tino1b2be/ST080/Docs/Case/Dimensions/instrument.png

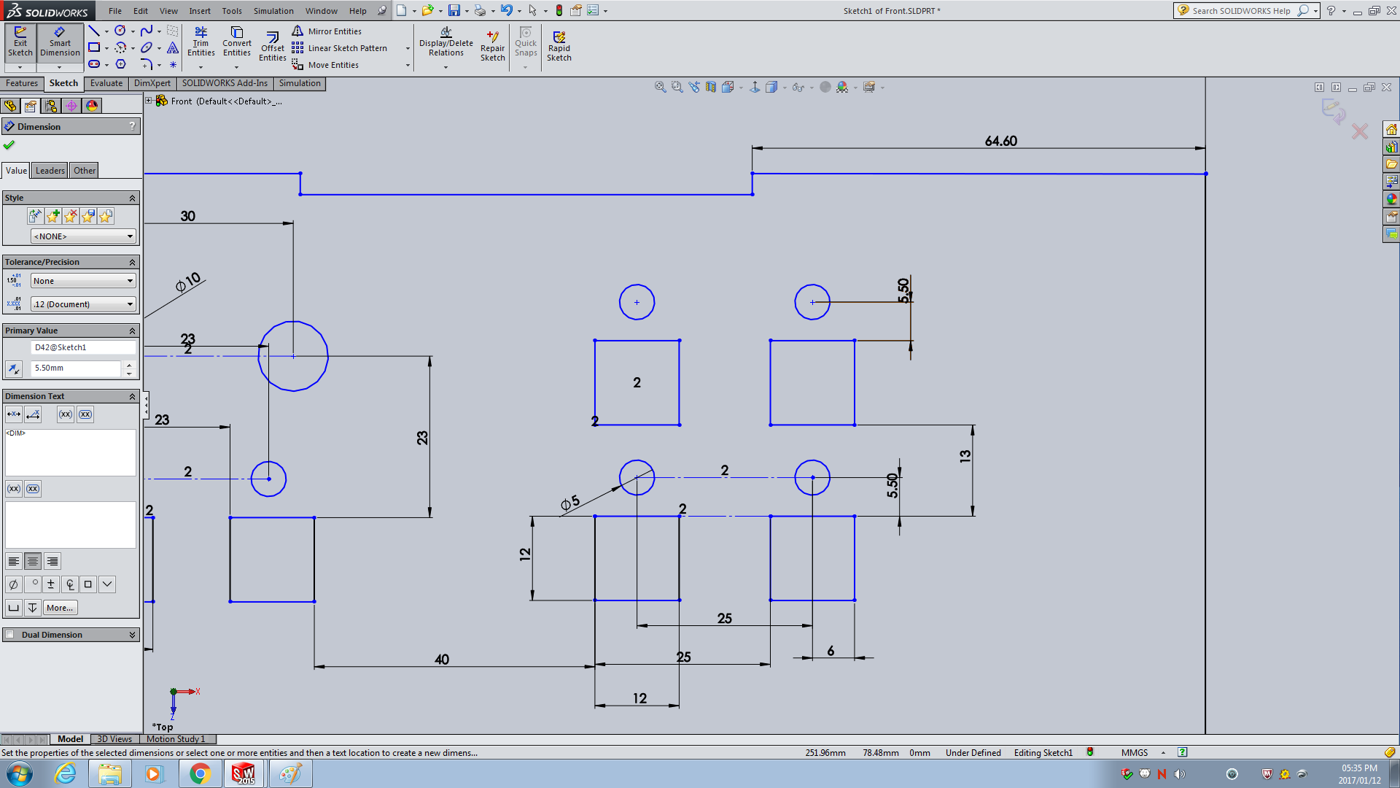
Docs/Case/Dimensions/instrument.png
