tino1b2be/ST080/Docs/Case/Dimensions/lcd.png

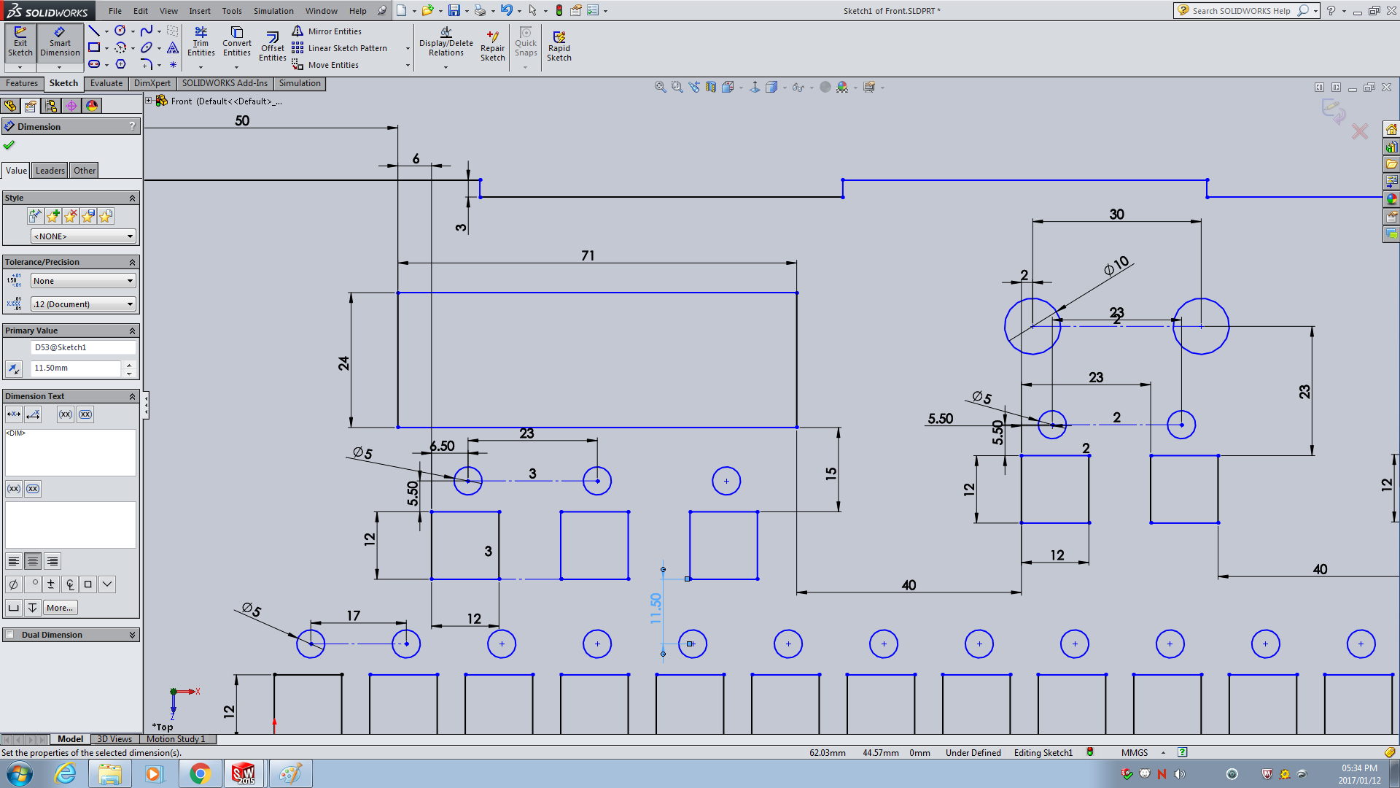
Docs/Case/Dimensions/lcd.png
