tino1b2be/ST080/Docs/Case/Dimensions/rack.png

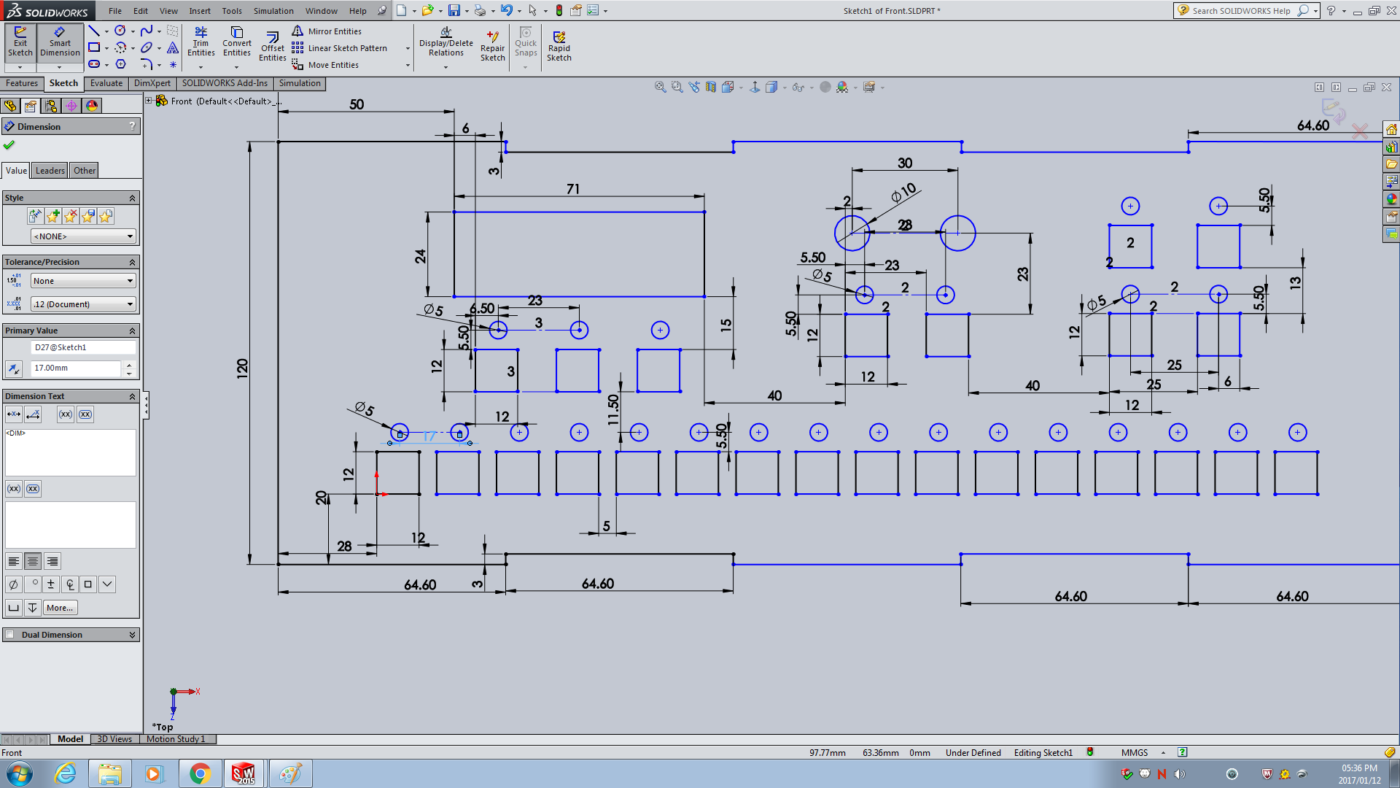
Docs/Case/Dimensions/rack.png
