tino1b2be/ST080/Docs/Case/Dimensions/tempo.png

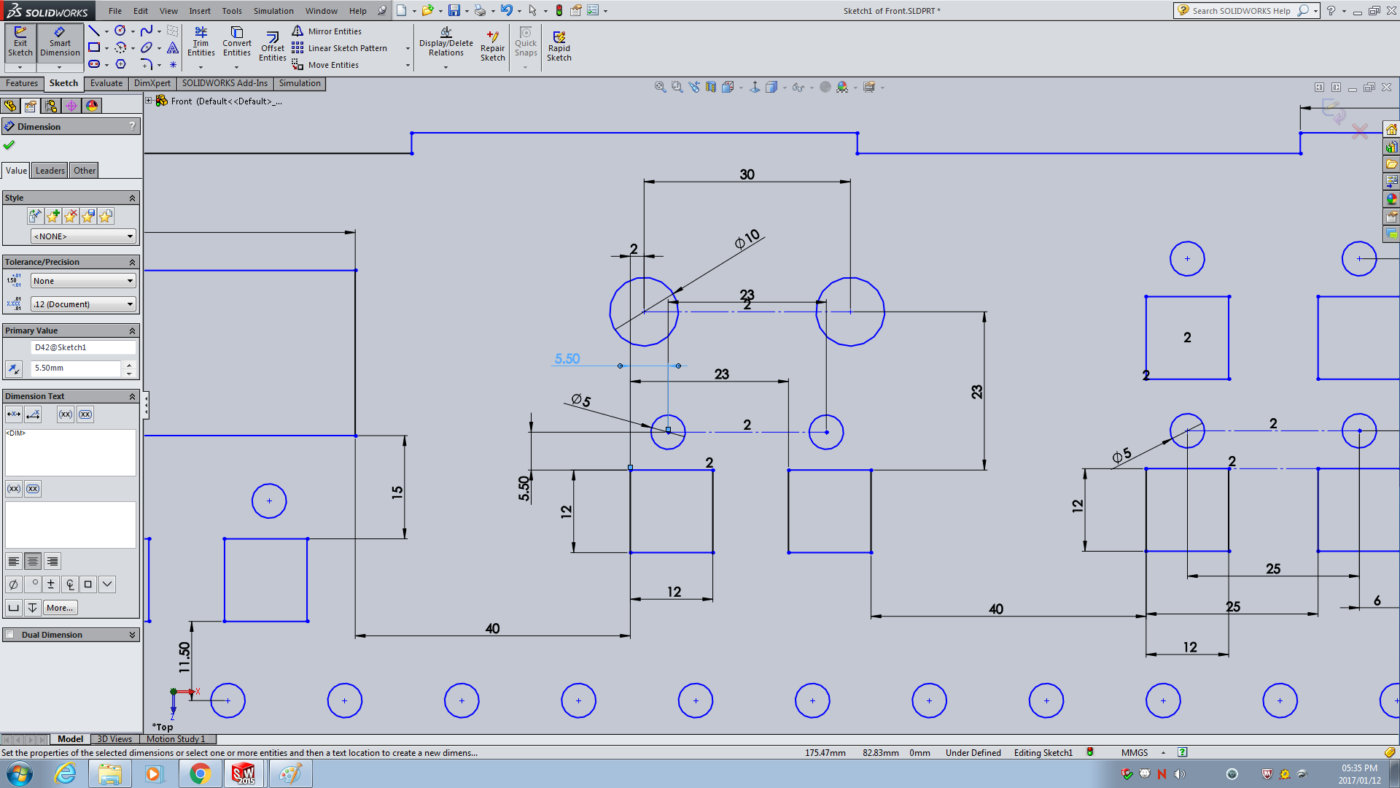
Docs/Case/Dimensions/tempo.png
