tino1b2be/ST080/Docs/Case/Dimensions/whole.png

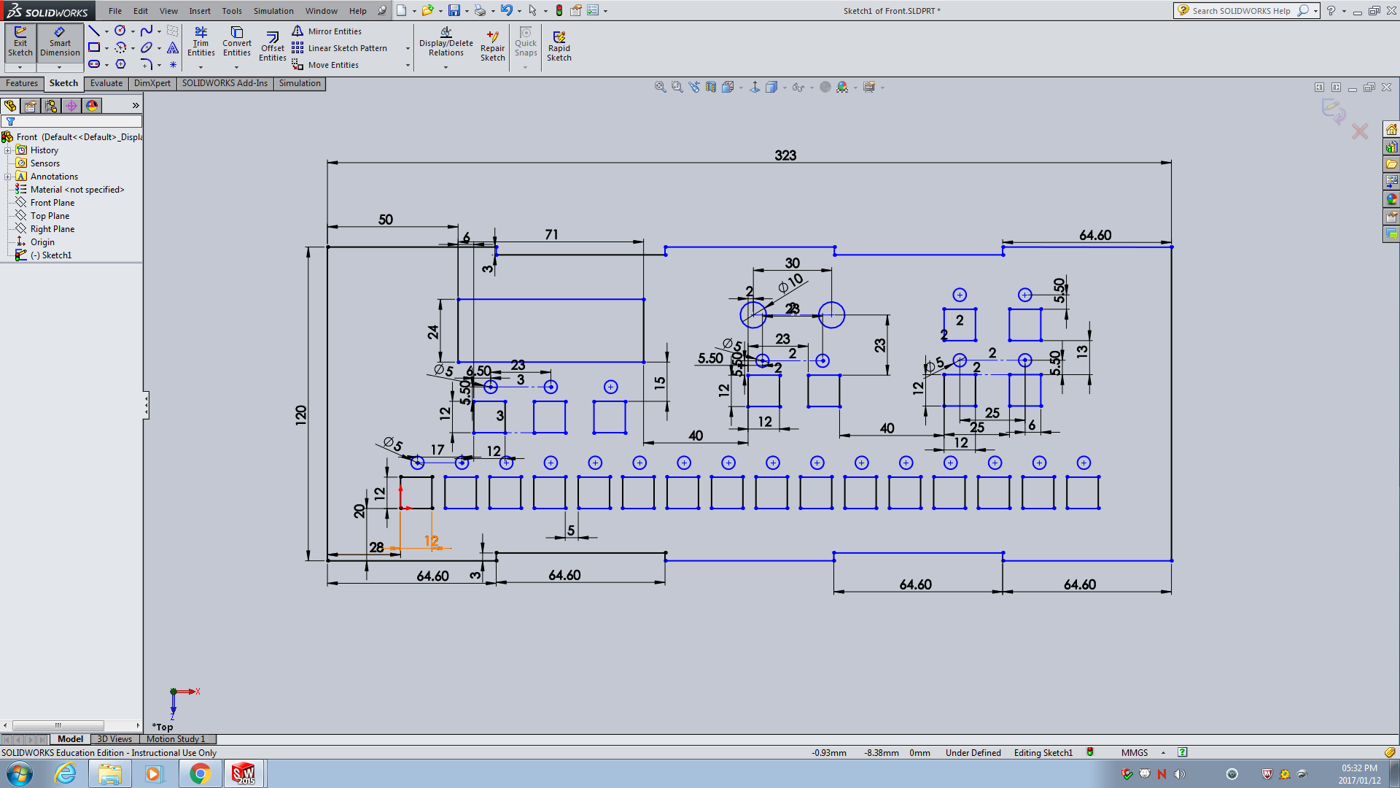
Docs/Case/Dimensions/whole.png
