tino1b2be/ST080/Docs/Case/Views/Back.PNG

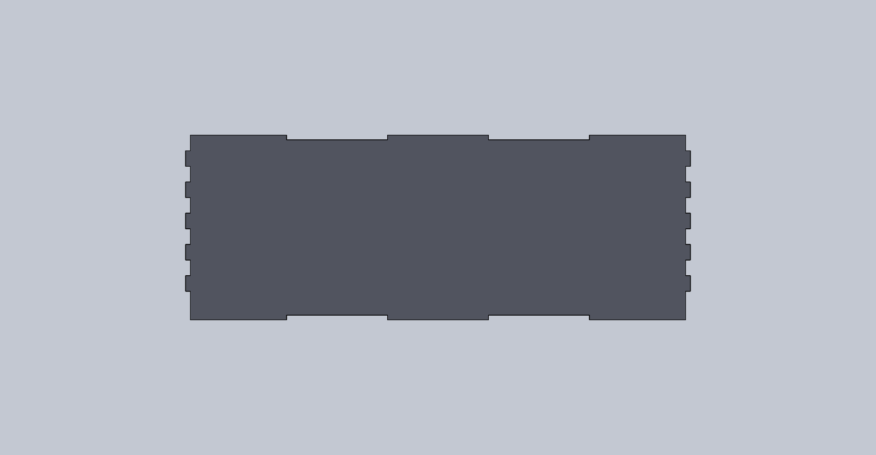
Docs/Case/Views/Back.PNG
