tino1b2be/ST080/Docs/Case/Views/Bottom.PNG

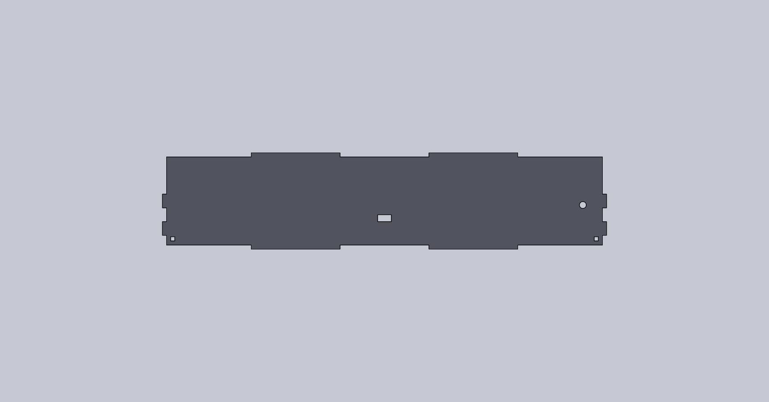
Docs/Case/Views/Bottom.PNG
