tino1b2be/ST080/Docs/Case/Views/Connector.PNG

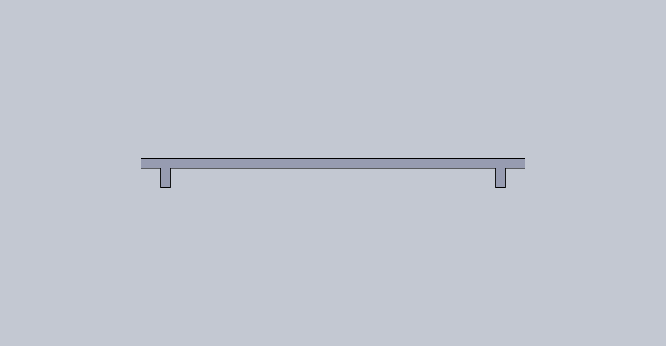
Docs/Case/Views/Connector.PNG
