tino1b2be/ST080/Docs/Case/Views/Left_Right.PNG

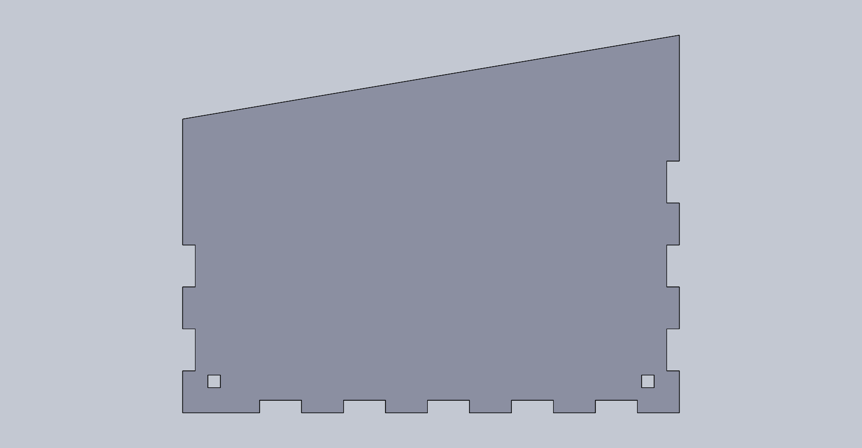
Docs/Case/Views/Left_Right.PNG
