tino1b2be/ST080/Docs/Case/Views/Top.PNG

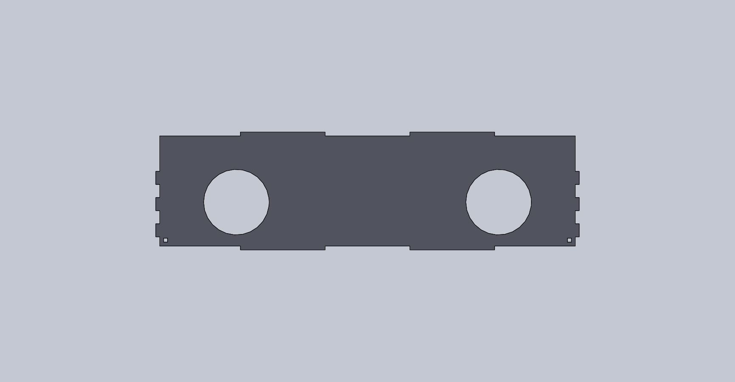
Docs/Case/Views/Top.PNG
