tino1b2be/ST080/Docs/Schematics/Audio-jack.png

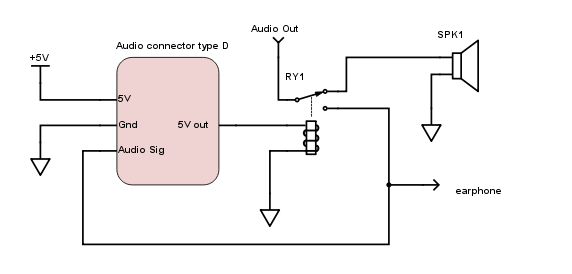
Docs/Schematics/Audio-jack.png
