tino1b2be/ST080/Docs/Schematics/Channel rack.png

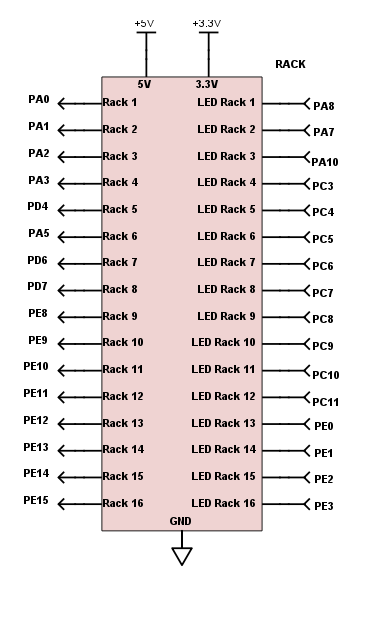
Docs/Schematics/Channel rack.png
