tino1b2be/ST080/Docs/Schematics/Eeprom-connection-STM32F4.png

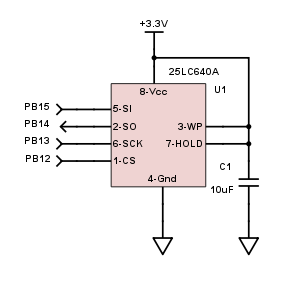
Docs/Schematics/Eeprom-connection-STM32F4.png
