tino1b2be/ST080/Docs/Schematics/Instruments.png

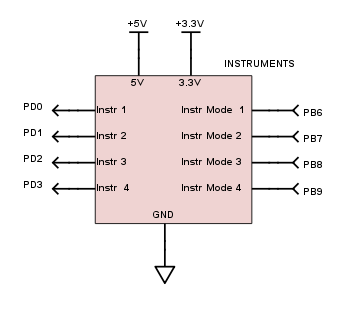
Docs/Schematics/Instruments.png
