tino1b2be/ST080/Docs/Schematics/Led circuit.png

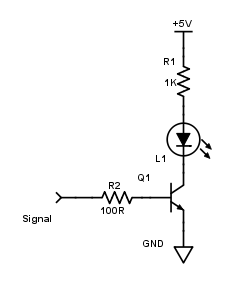
Docs/Schematics/Led circuit.png
