tino1b2be/ST080/Docs/Schematics/LM386-beeter-audio-amp.png

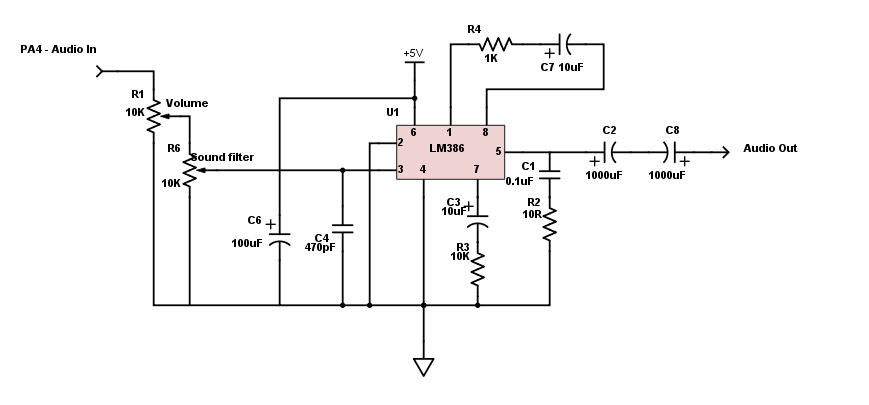
Docs/Schematics/LM386-beeter-audio-amp.png
