tino1b2be/ST080/Docs/Schematics/Mode.png

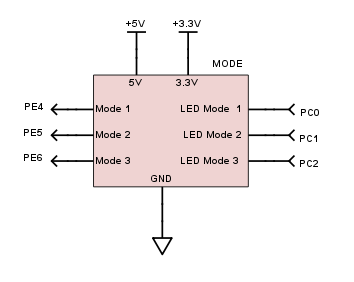
Docs/Schematics/Mode.png
