tino1b2be/ST080/Docs/Schematics/stm32F4-DISCOVERY.png

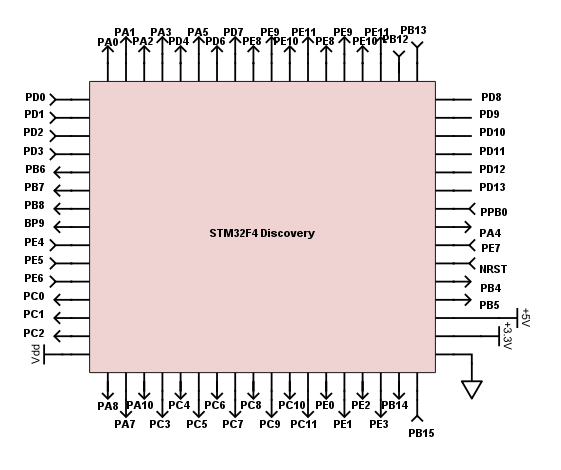
Docs/Schematics/stm32F4-DISCOVERY.png
