tino1b2be/ST080/Docs/Case/Assembly/Drumbeat machine 2 (1).PNG

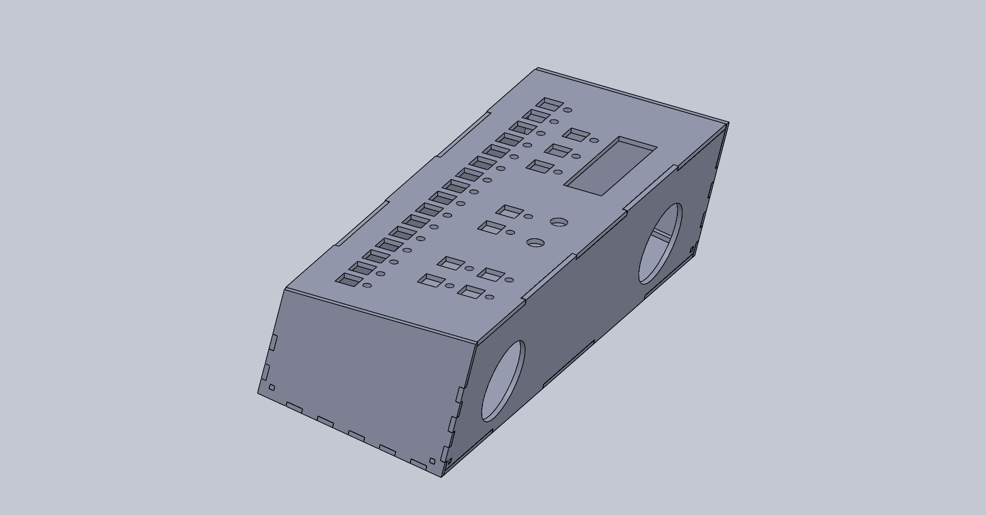
Docs/Case/Assembly/Drumbeat machine 2 (1).PNG
