tino1b2be/ST080/Docs/Case/Assembly/Drumbeat machine 3.PNG

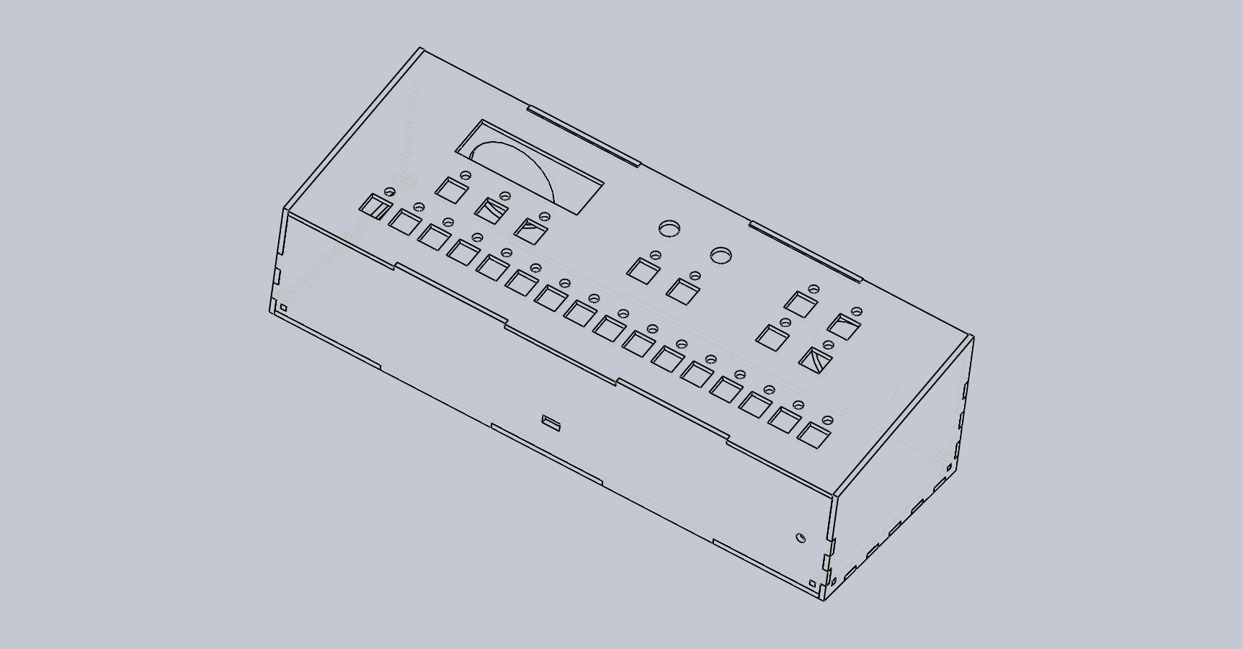
Docs/Case/Assembly/Drumbeat machine 3.PNG
