tino1b2be/ST080/Docs/Case/Assembly/Drumbeat machine.PNG

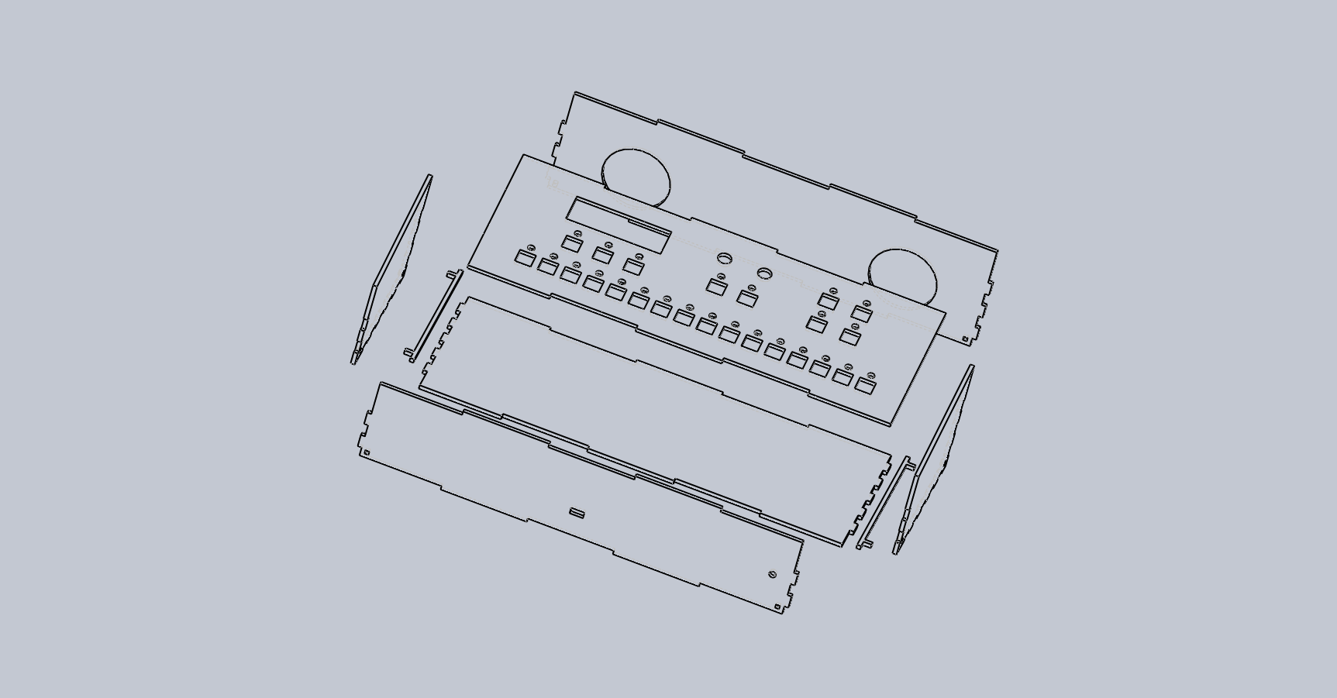
Docs/Case/Assembly/Drumbeat machine.PNG
