tino1b2be/ST080/Code/src/ST080/LCD/tm_stm32f4_hd44780.h

/**
 * @author  Tilen Majerle
 * @email   tilen@majerle.eu
 * @website http://stm32f4-discovery.com
 * @link    http://stm32f4-discovery.com/2014/06/library-16-interfacing-hd44780-lcd-controller-with-stm32f4/
 * @version v1.2
 * @ide     Keil uVision
 * @license GNU GPL v3
 * @brief   HD44780 LCD driver library for STM32F4xx
 *	
@verbatim
   ----------------------------------------------------------------------
    Copyright (C) Tilen Majerle, 2015
    
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
    You should have received a copy of the GNU General Public License
    along with this program.  If not, see <http://www.gnu.org/licenses/>.
   ----------------------------------------------------------------------
@endverbatim
 */
#ifndef TM_HD44780_H
#define TM_HD44780_H 120
/**
 * @addtogroup TM_STM32F4xx_Libraries
 * @{
 */

/**
 * @defgroup TM_HD44780
 * @brief    HD44780 LCD driver library for STM32F4xx - http://stm32f4-discovery.com/2014/06/library-16-interfacing-hd44780-lcd-controller-with-stm32f4/
 * @{
 *
 *	It also supports all HD44780 compatible LCD drivers.
 *
 *	\par Default pinout
 *	
@verbatim
LCD		STM32F4XX		DESCRIPTION

GND		GND				Ground
VCC		+5V				Power supply for LCD
V0		Potentiometer	Contrast voltage. Connect to potentiometer
RS		PB2				Register select, can be overwritten in your project's defines.h file
RW		GND				Read/write
E		PB7				Enable pin, can be overwritten in your project's defines.h file
D0		-				Data 0 - doesn't care
D1		-				Data 1 - doesn't care
D2		-				Data 2 - doesn't care
D3		-				Data 3 - doesn't  care
D4		PC12			Data 4, can be overwritten in your project's defines.h file
D5		PC13			Data 5, can be overwritten in your project's defines.h file
D6		PB12			Data 6, can be overwritten in your project's defines.h file
D7		PB13			Data 7, can be overwritten in your project's defines.h file
A		+3V3			Back light positive power
K		GND				Ground for back light
@endverbatim	
 *	
 * If you want to change pinout, do this in your defines.h file with lines below and set your own settings:
 *	
@verbatim
//RS - Register select pin
#define HD44780_RS_PORT     GPIOB
#define HD44780_RS_PIN      GPIO_PIN_2
//E - Enable pin
#define HD44780_E_PORT      GPIOB
#define HD44780_E_PIN       GPIO_PIN_7
//D4 - Data 4 pin
#define HD44780_D4_PORT     GPIOC
#define HD44780_D4_PIN      GPIO_PIN_12
//D5 - Data 5 pin
#define HD44780_D5_PORT     GPIOC
#define HD44780_D5_PIN      GPIO_PIN_13
//D6 - Data 6 pin
#define HD44780_D6_PORT     GPIOB
#define HD44780_D6_PIN      GPIO_PIN_12
//D7 - Data 7 pin
#define HD44780_D7_PORT     GPIOB
#define HD44780_D7_PIN      GPIO_PIN_13
@endverbatim
 *
 * \par Changelog
 *
@verbatim
 Version 1.2
  - March 11, 2015
  - Added support for my new GPIO library

 Version 1.1
  - November 08, 2014
  - D6 and D7 default pins changed from PC14,15 to PB12,13, because RTC crystal is on PC14,15
 
 Version 1.0
  - First release
@endverbatim
 *
 * \par Dependencies
 *
@verbatim
 - STM32F4xx
 - STM32F4xx RCC
 - defines.h
@endverbatim
 */
#include "stm32f4xx.h"
#include "stm32f4xx_rcc.h"
#include "stm32f4xx_gpio.h"
#include "../../TM38/tm_stm32f4_gpio.h"

/**
 * @defgroup TM_HD44780_Macros
 * @brief    Library defines
 * @{
 */

/* 4 bit mode */
/* Control pins, can be overwritten */
/* RS - Register select pin */
#ifndef HD44780_RS_PIN
#define HD44780_RS_PORT				GPIOD
#define HD44780_RS_PIN				GPIO_PIN_8
#endif
/* E - Enable pin */
#ifndef HD44780_E_PIN
#define HD44780_E_PORT				GPIOD
#define HD44780_E_PIN				GPIO_PIN_9
#endif
/* Data pins */
/* D4 - Data 4 pin */
#ifndef HD44780_D4_PIN
#define HD44780_D4_PORT				GPIOD
#define HD44780_D4_PIN				GPIO_PIN_10
#endif
/* D5 - Data 5 pin */
#ifndef HD44780_D5_PIN
#define HD44780_D5_PORT				GPIOD
#define HD44780_D5_PIN				GPIO_PIN_11
#endif
/* D6 - Data 6 pin */
#ifndef HD44780_D6_PIN
#define HD44780_D6_PORT				GPIOD
#define HD44780_D6_PIN				GPIO_PIN_12
#endif
/* D7 - Data 7 pin */
#ifndef HD44780_D7_PIN
#define HD44780_D7_PORT				GPIOD
#define HD44780_D7_PIN				GPIO_PIN_13
#endif

/**
 * @}
 */

/**
 * @defgroup TM_HD44780_Functions
 * @brief    Library Functions
 * @{
 */

/**
 * @brief  Initializes HD44780 LCD
 * @brief  cols: width of lcd
 * @param  rows: height of lcd
 * @retval None
 */
void TM_HD44780_Init(uint8_t cols, uint8_t rows);

/**
 * @brief  Turn display on
 * @param  None
 * @retval None
 */
void TM_HD44780_DisplayOn(void);

/**
 * @brief  Turn display off
 * @param  None
 * @retval None
 */
void TM_HD44780_DisplayOff(void);

/**
 * @brief  Clears entire LCD
 * @param  None
 * @retval None
 */
void TM_HD44780_Clear(void);

/**
 * @brief  Puts string on lcd
 * @param  x location
 * @param  y location
 * @param  *str: pointer to string to display
 * @retval None
 */
void TM_HD44780_Puts(uint8_t x, uint8_t y, char* str);

/**
 * @brief  Enables cursor blink
 * @param  None
 * @retval None
 */
void TM_HD44780_BlinkOn(void);

/**
 * @brief  Disables cursor blink
 * @param  None
 * @retval None
 */
void TM_HD44780_BlinkOff(void);

/**
 * @brief  Shows cursor
 * @param  None
 * @retval None
 */
void TM_HD44780_CursorOn(void);

/**
 * @brief  Hides cursor
 * @param  None
 * @retval None
 */
void TM_HD44780_CursorOff(void);

/**
 * @brief  Scrolls display to the left
 * @param  None
 * @retval None
 */
void TM_HD44780_ScrollLeft(void);

/**
 * @brief  Scrolls display to the right
 * @param  None
 * @retval None
 */
void TM_HD44780_ScrollRight(void);

/**
 * @brief  Creates custom character
 * @param  location: Location where to save character on LCD. LCD supports up to 8 custom characters, so locations are 0 - 7
 * @param *data: Pointer to 8-bytes of data for one character
 * @retval None
 */
void TM_HD44780_CreateChar(uint8_t location, uint8_t* data);

/**
 * @brief  Puts custom created character on LCD
 * @param  location: Location on LCD where character is stored, 0 - 7
 * @retval None
 */
void TM_HD44780_PutCustom(uint8_t x, uint8_t y, uint8_t location);

/**
 * @brief	Delay
 */
void LCD_Delay(uint32_t microseconds);

/**
 * @}
 */
 
/**
 * @}
 */

#endif
