tino1b2be/ST080/Code/src/FreestyleMode.h

/*
 * FreestyleMode.h
 *
 *  Created on: Sep 27, 2016
 *      Author: user
 */

#ifndef FREESTYLEMODE_H_
#define FREESTYLEMODE_H_

// TODO implement freestle stuff

void vFreestyleTask(void * pvparameterss);

#endif /* FREESTYLEMODE_H_ */
