tino1b2be/ST080/Code/src/PlaybackMode.h

/*
 * PlaybackMode.h
 *
 *  Created on: Sep 27, 2016
 *      Author: Tinotenda Chemvura
 */

#ifndef PLAYBACKMODE_H_
#define PLAYBACKMODE_H_

#include "Utils080.h"

void vPlaybackTask(void * pvparameters);

#endif /* PLAYBACKMODE_H_ */
