tino1b2be/ST080/Code/src/debug.h

/*
 * debug.h
 *
 *  Created on: Feb 9, 2011
 *      Author: James
 */

#ifndef DEBUG_H_
#define DEBUG_H_

void vDebugInitQueue( void );
void vDebugString( char *s );
void vDebugPrintf(const char *fmt, ...);
void vDebugPrintResetType( void );


#endif /* DEBUG_H_ */
