tino1b2be/ST080/Code/src/ST080/Utils080.h

#define UTILS080_H_
#include <stdbool.h>
#include <stdlib.h>
#include <math.h>
#include "TM38/defines.h"
#include "TM38/tm_stm32f4_disco.h"
#include "TM38/tm_stm32f4_exti.h"
#include "FreeRTOS.h"
#include "task.h"
#include "queue.h"
#include "semphr.h"
#include "stm32f4xx.h"
#include "stm32f4_discovery.h"
#include "LCD/tm_stm32f4_hd44780.h"
#include "Eeprom.h"
#include "Tempo.h"
uint64_t tickTime = 0;        // Counts OS ticks (default = 1000Hz).
uint64_t u64IdleTicks = 0;   // Value of u64IdleTicksCnt is copied once per sec.
uint64_t u64IdleTicksCnt = 0; // Counts when the OS has no task to execute.
uint16_t u16PWM1 = 0;
void vApplicationTickHook(void) {
	++tickTime;
}
void vApplicationIdleHook(void) {
	++u64IdleTicksCnt;
}
void vApplicationMallocFailedHook(void) {
	configASSERT(0);  				// Latch on any failure / error.
}
#define MODES_TASK_PRIORITY 1
#define UI_TASK_PRIORITY 2
#define GPIO_TASK_PRIORITY 3
#define MODES_STACK_SIZE 128
#define UI_STACK_SIZE 128
#define GPIO_STACK_SIZE 128
#define LCD_COLUMNS 16
#define LCD_ROWS 2
#define COMPOSER 1
#define PLAYBACK 2
#define FREESTYLE 3
#define SAVE 4
#define ERROR_MODE 5
#define ENTER 6
#define INSTR_1 0
#define INSTR_2 1
#define INSTR_3 2
#define INSTR_4 3
#define SAMPLE_SIZE 1103
#define DEFAULT_COMPOSER_BUFFERSIZE 20000
#define DEFAULT_TEMPO 0 // define proper tempo
#define CHANNEL_RACK_SIZE 1024
SEMAPHORE_H flags_lock = NULL;
bool PAD_STATE[4];  				//Global variable use to check the state of the Freestyle pad
bool STATE_CHANGED;					//Global variable to check if there has been a change in Pad status
uint8_t MODE = COMPOSER; 			// Global variable to e used to identify which mode the ST080 is currently in
bool status = true;					// Variable used by Composer to check if there has been an update on the channel rack configs.
uint64_t current = 0, previous = 0;	// Variables to be used by IRQ Handler for debouncing
uint8_t current_sample = INSTR_1;	// variable used by the composer mode to check which instrument sample is on the channel rack
uint8_t played_inst = 0;			// variable used by the Freestyle mode to determine the instrument(s) played
uint16_t freestyle_samples [11][SAMPLE_SIZE]; // This will hold the samples of the different possible combinations
bool channelRack[16][4][16]; 		// 16 channel racks with 4 instruments each with 16 beat channel
uint8_t currentBeat = 0;			// Variable to indicate the current beat/instrumental being edited on the beat rack.
bool resetLEDs = true;				// flag used to fresh the LEDs when switching modes. This flag will be checked by the UI_Task to check whether it should reset the LEDs or not
bool UPDATE_LCD = true; 				// flag used to update LCD
bool UPDATE_BEAT = true;			//flag used to update beat on LCD in playback mode
bool UPDATE_TEMPO = true;
uint16_t ComposerBuffer[DEFAULT_COMPOSER_BUFFERSIZE];		// Buffer used by the composer mode to push to the audio output interface
uint16_t tempo = DEFAULT_TEMPO;
uint16_t drumKit1 [4][SAMPLE_SIZE] = {
			{2085,2008,2095,2000,2101,2009,2382,2549,2753,2861,3050,2947,3447,3213,2841,3366,2539,2304,1732,1885,1638,890,336,708,0,826,1013,98,308,757,979,1337,1143,1224,2946,2101,2594,3308,2984,2768,2786,3686,3013,2882,3846,3073,2967,2544,2580,1637,2044,1984,1662,739,941,1676,604,1648,587,357,424,1398,1598,1469,1119,2209,2275,1294,2969,3090,2596,2642,3314,3407,3028,2973,3453,3889,2854,3188,2904,1660,3186,2475,1571,1899,1663,1717,1876,1270,743,947,977,1193,2047,664,847,1934,1832,2076,1032,2378,2015,2179,2374,2790,2061,2667,2939,2139,3117,2058,2930,2694,1867,1658,2807,1653,1754,2355,1458,1447,1604,1273,1383,2212,1511,1330,1819,1302,1826,2573,1830,2503,2092,2061,2202,3041,3166,2328,2587,2167,2691,3485,2193,2532,2582,2557,2366,1788,2071,1779,1599,1890,2410,1591,1260,842,1924,2105,1347,1307,1570,1510,1804,1678,1429,2268,2511,2005,1879,2062,2377,2604,2244,1946,2271,2708,2006,2665,2000,2331,2252,1807,2211,1366,2380,2045,1924,2308,1638,1645,1798,1824,1879,2131,1838,2260,1691,1947,2819,2344,2319,2012,2280,2276,2412,2140,2484,2356,2592,2525,1594,2612,2153,1922,1930,1933,1931,1546,2388,1787,1568,1598,1522,1722,2314,1551,1250,2295,1545,1973,1920,1965,2088,1813,1840,2243,2460,2176,2259,1969,1824,2866,2402,1991,2103,1928,2280,2347,2345,1909,2032,2011,2053,1991,2071,1590,2424,2073,1816,2155,1838,2502,1722,2183,2277,2051,1853,2232,2424,1662,2642,2103,2186,2371,1991,1956,1836,2542,1915,2123,1821,2139,2023,1797,1723,1778,2224,1562,1802,1903,2196,1480,2004,1999,1781,1946,1713,2094,2144,2089,2186,2072,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
void startUpConfigs(void); 			// Function to run the start up configurations.
void delay_ms(uint32_t milli);
void error_(void);					// function to flash the on-board LEDs when an error occurs
void lcd_flush_write(uint8_t row_num, char* msg);
void updateLED(uint8_t pin, bool On, uint8_t type); // implemented in UIUdate
LED_GPIO getGPIO(uint8_t pin, uint8_t type); // implemented in UIUdate
void loadFromEeprom(void);
void saveToEeprom(void);
void formatEeprom(void);
bool isChannelEmpty(uint8_t index);
void lcd_write(uint8_t col_num, uint8_t row_num, char* msg);
void select_beat(void);
void startUpConfigs(){
	TM_HD44780_Init(LCD_COLUMNS, LCD_ROWS);
	TM_HD44780_Clear();
	GPIO_SetBits(GPIOB, GPIO_PIN_5);
	lcd_write(4, 0, "WELCOME");
	lcd_write(5, 1, "ST080");
	RCC_APB2PeriphClockCmd(RCC_APB2Periph_SYSCFG, ENABLE);
	RCC_AHB1PeriphClockCmd(RCC_AHB1Periph_GPIOA, ENABLE);
	RCC_AHB1PeriphClockCmd(RCC_AHB1Periph_GPIOB, ENABLE);
	RCC_AHB1PeriphClockCmd(RCC_AHB1Periph_GPIOC, ENABLE);
	RCC_AHB1PeriphClockCmd(RCC_AHB1Periph_GPIOD, ENABLE);
	RCC_AHB1PeriphClockCmd(RCC_AHB1Periph_GPIOE, ENABLE);
	GPIO_InitTypeDef GPIO_InitStructure;
	GPIO_InitStructure.GPIO_Mode = GPIO_Mode_OUT;
	GPIO_InitStructure.GPIO_OType = GPIO_OType_PP;
	GPIO_InitStructure.GPIO_Speed = GPIO_Speed_100MHz;
	GPIO_InitStructure.GPIO_PuPd = GPIO_PuPd_DOWN;
	GPIO_InitStructure.GPIO_Pin = GPIO_Pin_7 | GPIO_Pin_8 | GPIO_Pin_10;
	GPIO_Init(GPIOA, &GPIO_InitStructure);
	GPIO_InitStructure.GPIO_Pin =  GPIO_Pin_4 | GPIO_Pin_5 | GPIO_Pin_6 | GPIO_Pin_7 | GPIO_Pin_8 | GPIO_Pin_9;
	GPIO_Init(GPIOB, &GPIO_InitStructure);
	GPIO_InitStructure.GPIO_Pin = GPIO_Pin_0 | GPIO_Pin_1 | GPIO_Pin_2 | GPIO_Pin_3 | GPIO_Pin_4 | GPIO_Pin_5 | GPIO_Pin_6 | GPIO_Pin_7 | GPIO_Pin_8 | GPIO_Pin_9 | GPIO_Pin_10 | GPIO_Pin_11;
	GPIO_Init(GPIOC, &GPIO_InitStructure);
	GPIO_InitStructure.GPIO_Pin = GPIO_Pin_0 | GPIO_Pin_1 | GPIO_Pin_2 | GPIO_Pin_3;
	GPIO_Init(GPIOE, &GPIO_InitStructure);
	GPIO_SetBits(GPIOB, GPIO_PIN_5);
	GPIO_InitStructure.GPIO_Mode = GPIO_Mode_IN;		// Input mode
	GPIO_InitStructure.GPIO_OType = GPIO_OType_PP;		// Push - Pull
	GPIO_InitStructure.GPIO_PuPd = GPIO_PuPd_DOWN;		// To detect a logic high
	GPIO_InitStructure.GPIO_Pin = GPIO_PIN_4 | GPIO_PIN_6 | GPIO_PIN_7;;
	GPIO_Init(GPIOD, &GPIO_InitStructure);
	GPIO_InitStructure.GPIO_Pin = GPIO_PIN_0 | GPIO_PIN_1 | GPIO_PIN_2 | GPIO_PIN_3 | GPIO_PIN_5;
	GPIO_Init(GPIOA, &GPIO_InitStructure);
	GPIO_InitStructure.GPIO_Pin = GPIO_PIN_8 | GPIO_PIN_9 | GPIO_PIN_10 | GPIO_PIN_11 | GPIO_PIN_12 | GPIO_PIN_13 | GPIO_PIN_14 | GPIO_Pin_15;
	GPIO_Init(GPIOE, &GPIO_InitStructure);
	bool fail = false;
	if (TM_EXTI_Attach(GPIOD, GPIO_Pin_0, TM_EXTI_Trigger_Rising) != TM_EXTI_Result_Ok){
		fail = true;
	} else if (TM_EXTI_Attach(GPIOD, GPIO_Pin_1, TM_EXTI_Trigger_Rising) != TM_EXTI_Result_Ok){
		fail = true;
	} else if (TM_EXTI_Attach(GPIOD, GPIO_Pin_2, TM_EXTI_Trigger_Rising) != TM_EXTI_Result_Ok){
		fail = true;
	} else if (TM_EXTI_Attach(GPIOD, GPIO_Pin_3, TM_EXTI_Trigger_Rising) != TM_EXTI_Result_Ok){
		fail = true;
	} else if (TM_EXTI_Attach(GPIOE, GPIO_Pin_4, TM_EXTI_Trigger_Rising) != TM_EXTI_Result_Ok){
		fail = true;
	} else if (TM_EXTI_Attach(GPIOE, GPIO_Pin_5, TM_EXTI_Trigger_Rising) != TM_EXTI_Result_Ok){
		fail = true;
	} else if (TM_EXTI_Attach(GPIOE, GPIO_Pin_6, TM_EXTI_Trigger_Rising) != TM_EXTI_Result_Ok){
		fail = true;
	} else if (TM_EXTI_Attach(GPIOE, GPIO_Pin_7, TM_EXTI_Trigger_Rising) != TM_EXTI_Result_Ok){
		fail = true;
	}
	if (fail){
		error_();
	}
	EEPROM_Configuration();
	loadFromEeprom();		// Load the channel rack from the eeprom
	Tempo_Configuration();
	select_beat();
	GPIO_ResetBits(GPIOB, GPIO_PIN_5);
}
void TM_EXTI_Handler(uint16_t GPIO_Pin) {
	current = tickTime;
	if ((current - previous) < 30) {
		previous = current;
		return;
	}
	if (GPIO_Pin == GPIO_Pin_0) {
		if (MODE == COMPOSER){
			current_sample = INSTR_1;
			UPDATE_LCD = true;
		}
		else if (MODE == FREESTYLE) {
			PAD_STATE[0] = true;
			STATE_CHANGED = true;
			played_inst = played_inst + 2;
		}
	}
	else if (GPIO_Pin == GPIO_Pin_1) {
		if (MODE == COMPOSER){
			current_sample = INSTR_2;
			UPDATE_LCD = true;
		}
		else if (MODE == FREESTYLE) {
			PAD_STATE[1] = true;
			STATE_CHANGED = true;
			played_inst = played_inst + 4;
		}
	}
	else if (GPIO_Pin == GPIO_Pin_2) {
		if (MODE == COMPOSER){
			current_sample = INSTR_3;
			UPDATE_LCD = true;
		}
		else if (MODE == FREESTYLE) {
			PAD_STATE[2] = true;
			STATE_CHANGED = true;
			played_inst = played_inst + 8;
		}
	}
	else if (GPIO_Pin == GPIO_Pin_3) {
		if (MODE == COMPOSER){
			current_sample = INSTR_4;
			UPDATE_LCD = true;
		}
		else if (MODE == FREESTYLE) {
			PAD_STATE[3] = true;
			STATE_CHANGED = true;
			played_inst = played_inst + 16;
		}
	}
	else if (GPIO_Pin == GPIO_Pin_4) {
		MODE = COMPOSER;
		status = true;
		resetLEDs = true;
		UPDATE_LCD = true;
	}
	else if (GPIO_Pin == GPIO_Pin_5) {
		MODE = PLAYBACK;
		resetLEDs = true;
		UPDATE_LCD = true;
	}
	else if (GPIO_Pin == GPIO_Pin_6) {
		UPDATE_LCD = true;
		MODE = FREESTYLE;
		resetLEDs = true;
	}
	else if (GPIO_Pin == GPIO_Pin_7) {
		if (MODE == COMPOSER || MODE == PLAYBACK) {
			MODE = SAVE;
			status = true;
			resetLEDs = true;
			UPDATE_LCD = true;
		}
	}
	previous = current; // for debouncing
}
void lcd_flush_write(uint8_t row_num, char* msg){
	TM_HD44780_Clear();
	TM_HD44780_Puts(0,row_num,msg);
}
void lcd_write(uint8_t col_num, uint8_t row_num, char* msg){
	TM_HD44780_Puts(col_num,row_num,msg);
}
void saveToEeprom(){
	int i,j,k,l=0;
	uint8_t temp = 0;
	for (i = 0; i < 16; ++i) {
		for (j = 0; j < 4; ++j) {
			for (k = 0; k < 16; ++k, ++l) {
				temp = (uint8_t) channelRack[i][j][k];
				EEPROM_Write(l, temp);
			}
		}
	} // end of for loops
}// end of saveToEeprom
void formatEeprom(){
	int i,j,k,l=0;
	for (i = 0; i < 16; ++i) {
		for (j = 0; j < 4; ++j) {
			for (k = 0; k < 16; ++k, ++l) {
				EEPROM_Write(l, 0);
			}
		}
	} // end of for loops
}// end of saveToEeprom
void loadFromEeprom(){
	int i, j, k, l = 0;
	bool temp = false;
	for (i = 0; i < 16; ++i) {
		for (j = 0; j < 4; ++j) {
			for (k = 0; k < 16; ++k, ++l) {
				temp = (bool) EEPROM_Read(l);
				channelRack[i][j][k] = temp;
			}
		}
	} // end of for loops
} // end of loadFromEeprom
bool isChannelEmpty(uint8_t index){
	int j,k=0;
	for (j=0;j<4;++j){
		for (k=0;k<16;++k){
			if(channelRack[index][j][k]!=0){
				return false;
			}
		}
	}
	return true;
}
void delay_ms(uint32_t milli)
{
	uint32_t delay = milli * 17612;              // approximate loops per ms at 168 MHz, Debug config
	for(; delay != 0; delay--);
}
void select_beat(){
	lcd_flush_write(1, "Select a song!");
	lcd_write(5, 0, "ST080");
	MODE=ENTER;
}
void error_(void)
{
	MODE = ERROR_MODE;
	STM_EVAL_LEDInit(LED3);
	STM_EVAL_LEDInit(LED4);
	STM_EVAL_LEDInit(LED5);
	STM_EVAL_LEDInit(LED6);
	STM_EVAL_LEDOff(LED3);
	STM_EVAL_LEDOff(LED4);
	STM_EVAL_LEDOn(LED5);
	STM_EVAL_LEDOn(LED6);
	lcd_flush_write(0, "ERROR! Reset device");
	GPIO_SetBits(GPIOB, 6);
	GPIO_SetBits(GPIOB, 7);
	GPIO_SetBits(GPIOB, 8);
	GPIO_SetBits(GPIOB, 9);
	while(1){
		delay_ms(500);
		STM_EVAL_LEDToggle(LED3);
		STM_EVAL_LEDToggle(LED4);
		STM_EVAL_LEDToggle(LED5);
		STM_EVAL_LEDToggle(LED6);
	}
}
