tino1b2be/ST080/Code/src/ST080Utils.h

/**
	ST080 Utils header
*/


#ifndef ST080Utils_H_
#define ST080Utils_H_

// ==========================================================================================
// ======================= GLOBAL IMPORTS ===================================================
// ==========================================================================================

// other stuff
#include <stdbool.h>

// FreeRTOS stuff
#include "FreeRTOS.h"
#include "task.h"
#include "queue.h"
#include "semphr.h"

// STM32f4 stuff
#include "stm32f4xx.h"
#include "stm32f4_discovery.h"
#include "debug.h"
#include "mems.h"

// ==========================================================================================
// ================================== "static" functions ====================================
// ==========================================================================================

// Random functions
#define ABS(x)                           (x < 0) ? (-x) : x
#define MAX(a,b)                         (a < b) ? (b) : a
#define MIN(a,b)                         (a < b) ? (a) : b

// ==========================================================================================
// ============================ FreeRTOS stuff ==============================================
// ==========================================================================================

uint64_t tickTime = 0;        // Counts OS ticks (default = 1000Hz).
uint64_t u64IdleTicks = 0;   // Value of u64IdleTicksCnt is copied once per sec.
uint64_t u64IdleTicksCnt = 0; // Counts when the OS has no task to execute.
uint16_t u16PWM1 = 0;

// This FreeRTOS callback function gets called once per tick (default = 1000Hz).
// ----------------------------------------------------------------------------
void vApplicationTickHook(void) {
	++tickTime;
}

// This FreeRTOS call-back function gets when no other task is ready to execute.
// On a completely unloaded system this is getting called at over 2.5MHz!
// ----------------------------------------------------------------------------
void vApplicationIdleHook(void) {
	++u64IdleTicksCnt;
}

// A required FreeRTOS function.
// ----------------------------------------------------------------------------
void vApplicationMallocFailedHook(void) {
	configASSERT(0);  // Latch on any failure / error.
}


// ==========================================================================================
// ====================================== STRUCTS ===========================================
// ==========================================================================================

// constansts declarations
#define SAMPLE_SIZE 5000
#define NUM_INSTR 9

uint16_t samples[NUM_INSTR][SAMPLE_SIZE] = { /*total size = 90 k.bytes */
/*clap*/		{0.15350,-0.21951,-0.99997,-0.37451,0.14114,0.58893,0.01520,0.28497,0.35397,-0.40845,-0.84277,0.30164,0.01370,0.32178,0.47925,-0.28934,0.60480,-0.24963,-0.76624,-0.34360,0.02682,0.23880,0.78067,-0.03357,-0.15518,0.09818,-0.14026,-0.30383,-0.10806,0.01523,0.08566,0.39972,0.50589,0.19968,-0.35797,-0.30975,-0.25760,-0.20670,-0.23846,-0.02649,0.01968,0.24933,0.39612,0.90530,0.33621,0.10284,-0.19275,-0.44415,-0.58820,-0.55035,-0.06656,-0.34653,0.35611,0.20969,0.14676,0.17151,0.25592,0.31305,0.08951,0.09381,-0.25369,-0.34506,-0.07352,0.04132,0.32455,0.54282,0.08310,-0.21149,-0.10620,-0.16913,-0.16177,-0.15265,-0.24747,-0.18961,-0.10233,0.17731,0.13586,0.32318,0.30743,0.20493,0.22675,0.17047,-0.05475,-0.27051,-0.33994,-0.42581,-0.11084,-0.06540,0.03534,0.03561,-0.13028,-0.03256,0.33295,0.43356,0.22867,0.14966,-0.00925,-0.23703,0.07916,0.34274,0.09058,-0.27319,-0.44684,-0.24414,-0.03543,0.06836,-0.07864,-0.12228,-0.06482,-0.06061,-0.03259,0.19604,0.16357,0.14075,0.24780,0.00406,0.10535,-0.01886,-0.02820,0.12668,0.01657,0.00168,-0.12454,-0.07455,-0.05557,-0.07455,-0.01990,0.09137,-0.04050,-0.09665,0.01178,-0.05417,0.01532,0.04706,0.08032,0.05206,-0.03027,0.00061,0.02393,0.07727,0.00613,0.08319,0.23477,-0.02496,-0.64661,-0.24307,0.70236,0.07355,-0.70941,-0.25961,-0.21698,0.21078,0.99997,-0.01105,-0.43701,-0.57578,-0.30771,0.16550,0.55972,0.63562,-0.16779,-0.34290,-1.00000,-0.21677,0.94662,0.96329,0.66544,0.26657,-0.20761,-0.70352,-0.75635,-1.00000,-0.97095,-0.05859,0.33768,0.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
,-0.00919,-0.01086,-0.01694,-0.01050,-0.00104,0.00757,0.01337,0.01212,0.01212,0.00909,0.00308,-0.00815,-0.00638,-0.00247,-0.00470,-0.00027,0.00137,0.00247,0.00214,0.00415,0.00763,0.01315,0.01099,0.00543,-0.00183,-0.01297,-0.01349,-0.00891,-0.00922,-0.00858,-0.00421,-0.00195,0.00354,0.01205,0.01276,0.01205,0.01068,0.00797,0.00861,0.00595,0.00140,-0.00485,-0.00790,-0.00671,-0.00562,-0.00629,-0.00168,-0.00394,-0.01236,-0.01187,-0.01028,-0.00452,-0.00500,0.00189,0.00949,0.01303,0.01883},
/*cowbell*/		{0.13559,0.67523,0.99997,0.98682,0.88855,0.75436,0.36328,0.06573,-0.55911,-0.67258,-0.99991,-1,-0.99991,-1,0.8074,0.99997,0.99997,0.99997,0.99997,0.99997,0.99997,0.32086,-1,-1,-0.99991,-1,-0.99991,0.99994,0.99997,0.99997,0.99997,0.99997,0.99997,0.99997,0.99997,0.66974,-1,-1,-1,-1,-1,-1,-1,-0.99997,-0.25861,0.99997,0.99994,0.99997,0.99997,0.99997,0.99997,0.99997,0.99991,0.99997,-0.74411,-1,-0.99997,-1,-0.99994,-1,-1,-1,-1,-1,-0.39136,0.99997,0.99997,0.99997,0.99997,0.99997,0.99997,0.99997,0.99997,0.99997,0.99997,0.05267,-0.99994,-1,-1,-1,-0.99997,-1,-0.99991,-1,0.599,0.99991,0.99997,0.99991,0.99997,0.99991,0.99997,0.99991,0.99997,0.24475,-0.99994,-1,-1,-0.99994,-1,-0.99994,-1,-0.99994,0.00027,0.99997,0.99997,0.99994,0.99997,0.99994,0.99997,0.99997,0.99994,0.99997,-0.80542,-0.99994,-1,-1,-1,-0.99997,-1,-0.99991,-1,-0.99988,0.23001,0.99997,0.99997,0.99997,0.99997,0.99997,0.99997,0.99997,0.99997,0.99997,0.99997,-0.6311,-0.99997,-1,-0.99997,-1,-1,-1,-1,-0.99997,0.97931,0.99994,0.99997,0.99991,0.99997,0.99997,0.99997,0.99997,0.99997,-0.04694,-1,-1,-0.99997,-1,-0.99994,-1,-1,-0.99994,0.27493,0.99997,0.99997,0.99994,0.99997,0.99997,0.99994,0.99997,0.99997,0.99997,-0.49542,-1,-1,-0.99997,-1,-0.99997,-1,-1,-0.99997,-1,0.08078,0.99997,0.99994,0.99997,0.99991,0.99997,0.99997,0.99997,0.99997,0.99997,0.99994,-0.41013,-1,-1,-0.99997,-1,-1,-0.99994,-1,-0.99994,0.69711,0.99997,0.99997,0.99997,0.99997,0.99997,0.99997,0.99997,0.99994,0.0076,-1,-1,-0.99997,-1,-1,-0.99997,-1,-0.99997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
